dillpikos/Portable-WeatherStation-PCB-V1.0/images/rtcModuleFootprint.png

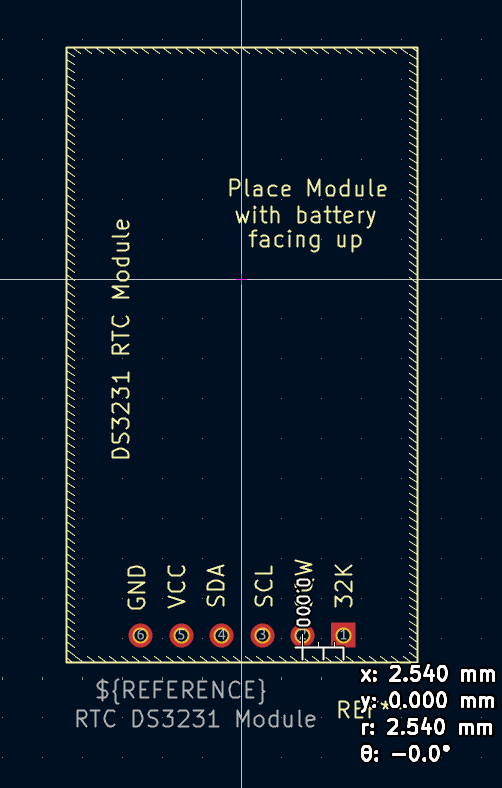
images/rtcModuleFootprint.png
