dillpikos/Portable-WeatherStation-PCB-V1.0/images/weatherStation3DBack.png

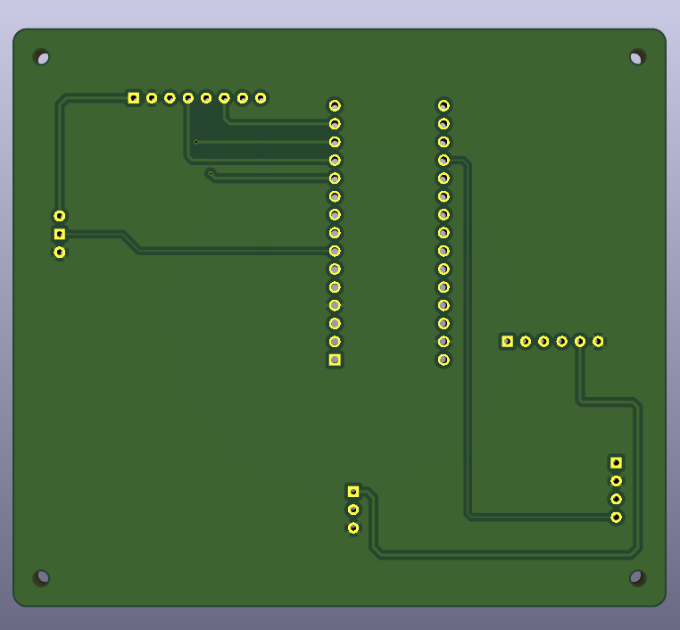
images/weatherStation3DBack.png
